sparkfunX/Artemis_Global_Tracker/img/ZOE-M8Q_Mask.JPG

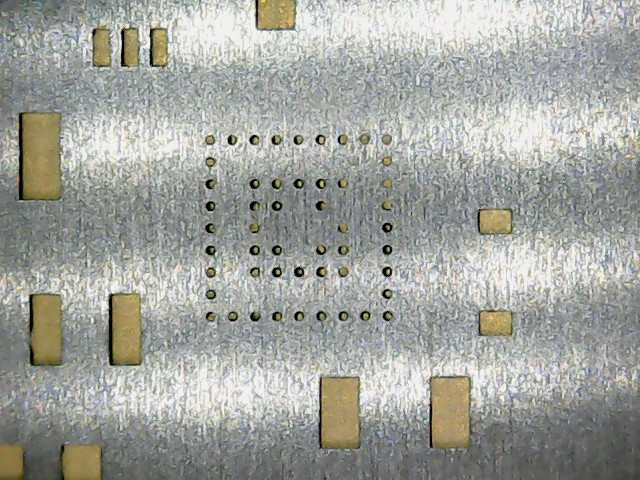
img/ZOE-M8Q_Mask.JPG
