sparkfunX/Artemis_Global_Tracker/img/ZOE-M8Q_Placed.JPG

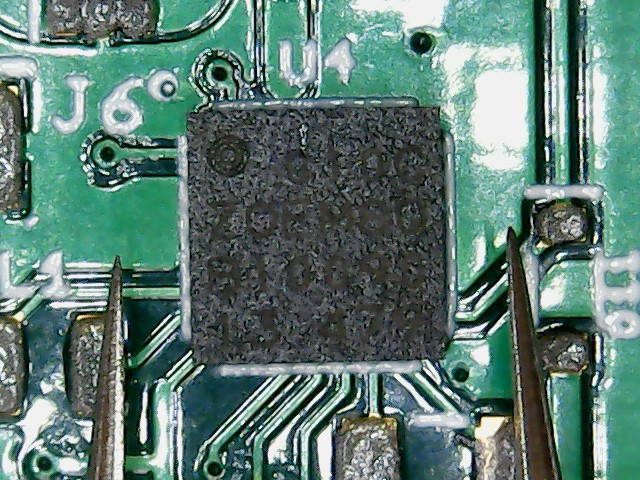
img/ZOE-M8Q_Placed.JPG
